rmcl/sailface/3dmodels/hull-experiments/hulltest7.FCStd

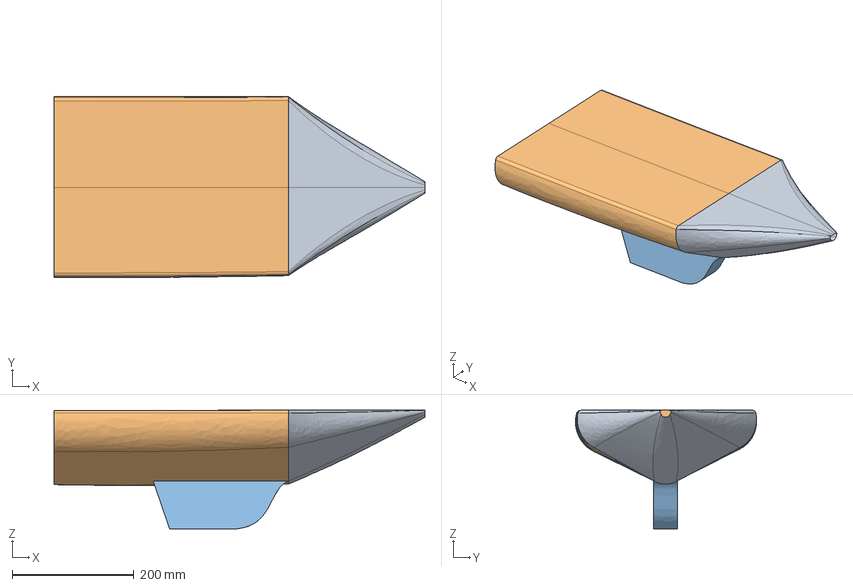
[picture p18: CAD file, 2022-07-22]
3dmodels/hull-experiments/hulltest7.FCStd
610.0 x 297.8 x 195.0 mm
KeelExtrude
