rmcl/sailface/3dmodels/hull-experiments/hulltest5.FCStd

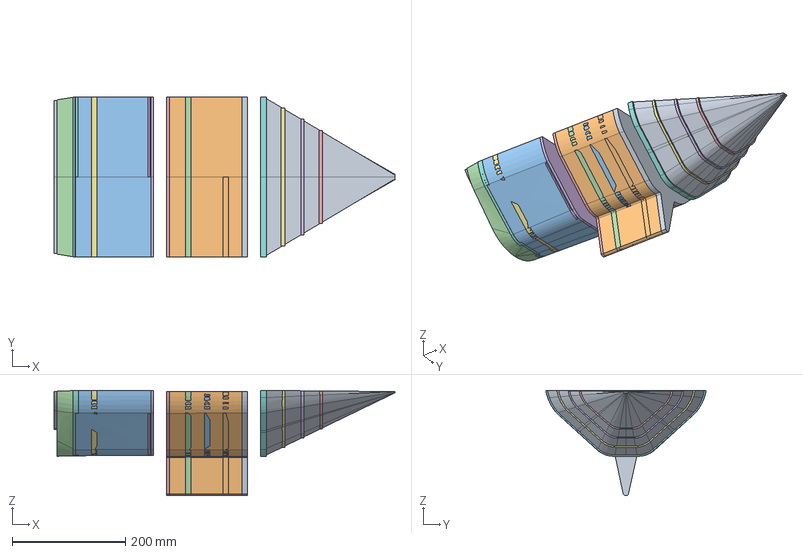
[picture p19: CAD file, 2022-07-22]
3dmodels/hull-experiments/hulltest5.FCStd
601.8 x 283.0 x 185.5 mm
