rmcl/sailface/3dmodels/Battery_VoltaicV70.FCStd

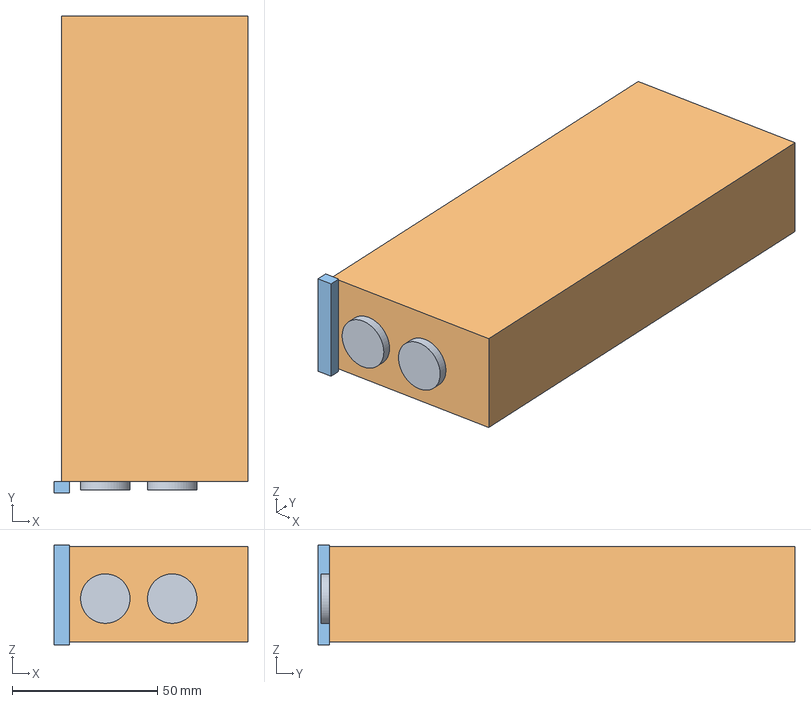
[picture p20: CAD file, 2022-07-22]
3dmodels/Battery_VoltaicV70.FCStd
66.6 x 164.0 x 34.3 mm
