rmcl/sailface/3dmodels/hull-experiments/hulltest8.FCStd

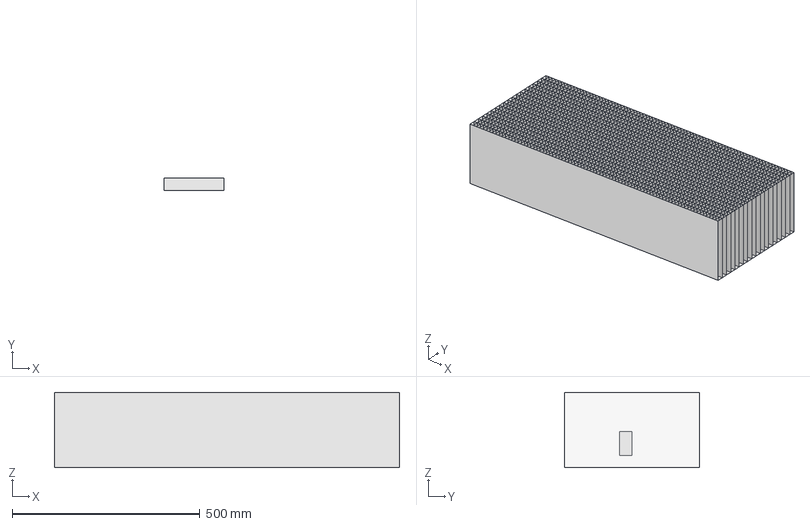
[picture p21: CAD file, 2022-07-22]
3dmodels/hull-experiments/hulltest8.FCStd
920.0 x 360.0 x 200.0 mm
battery
ExtrudeHullCrossectionSternBow
