rmcl/sailface/3dmodels/ServoSunFinderSF3218MG_v2.FCStd

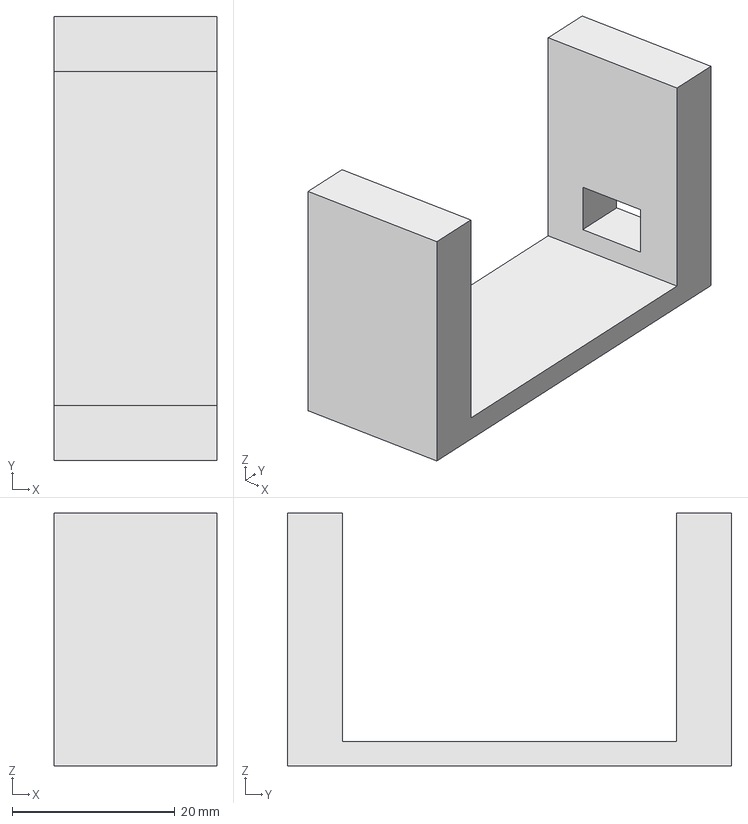
[picture p22: CAD file, 2022-07-22]
3dmodels/ServoSunFinderSF3218MG_v2.FCStd
20.0 x 54.5 x 31.0 mm
