rmcl/sailface/3dmodels/Prop_uxcell_prop_shaft.FCStd

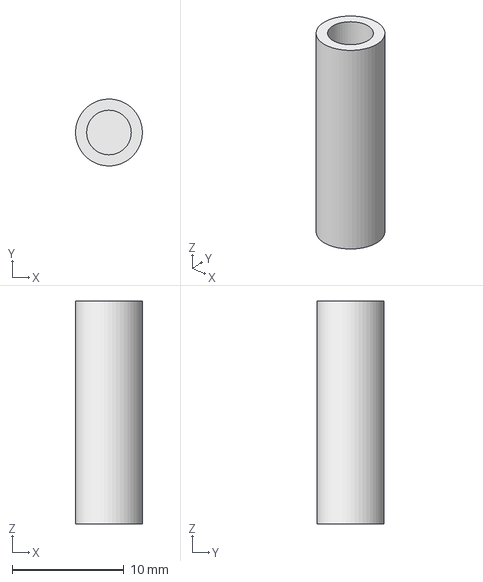
[picture p23: CAD file, 2022-07-22]
3dmodels/Prop_uxcell_prop_shaft.FCStd
5.99 x 6.00 x 20.0 mm
