rmcl/sailface/3dmodels/sunfounder_20kgSLDPRT.SLDPRT

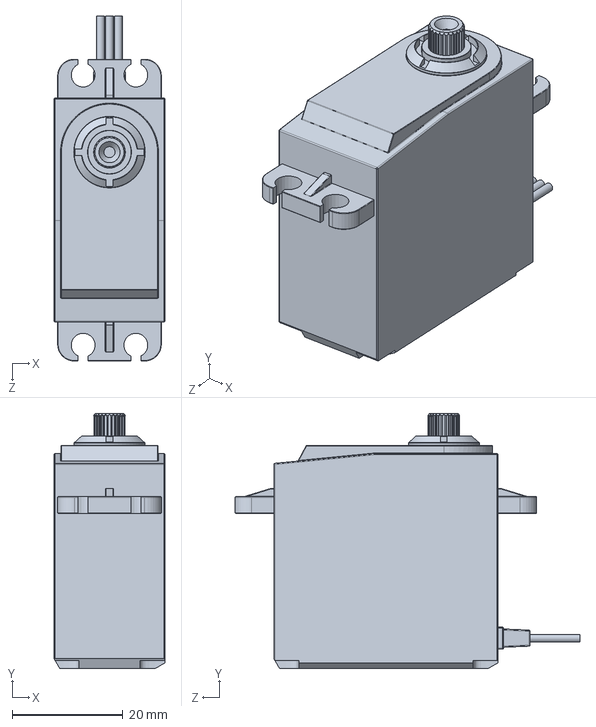
[picture p24: CAD file, 2022-07-22]
3dmodels/sunfounder_20kgSLDPRT.SLDPRT
20.0 x 46.0 x 62.2 mm
