rmcl/sailface/3dmodels/MotorHolderConnect_v1.FCStd

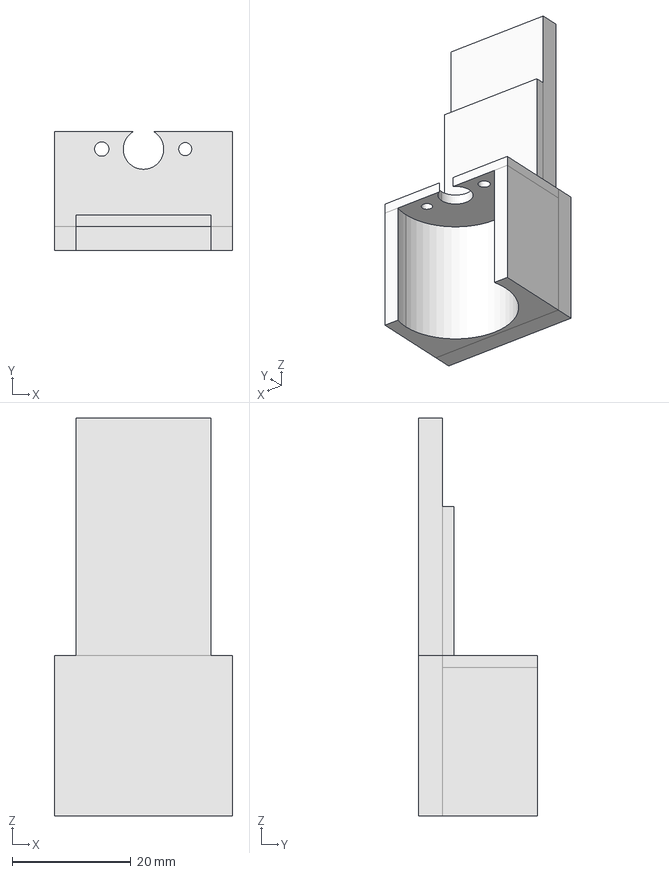
[picture p25: CAD file, 2022-07-22]
3dmodels/MotorHolderConnect_v1.FCStd
30.0 x 20.0 x 66.9 mm
