rmcl/sailface/3dmodels/internalstructure.FCStd

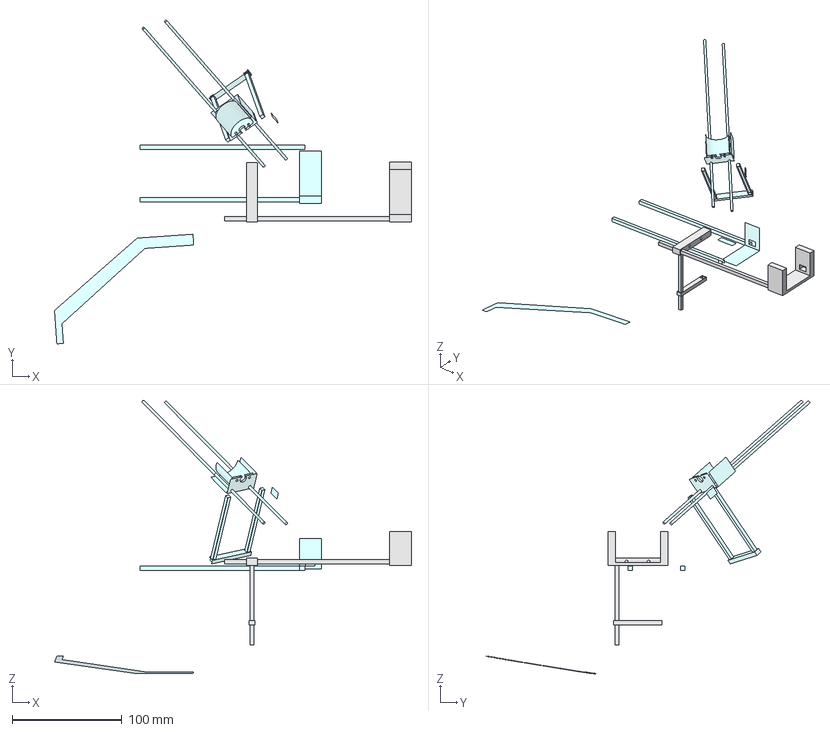
[picture p26: CAD file, 2022-07-22]
3dmodels/internalstructure.FCStd
324.8 x 294.6 x 248.7 mm
Element
Element001
Element002
Element003
Element004
Element005
Element006
Element007
Element008
Element009
Element011
Element014
Element015
Element018
_Element
_Element024
_Element026
_Element028
_Element030
_Element031
_Element032
_Element033
_Element034
_Element035
_Element037
_Element039
_Element041
_Element044
_Element046
_Element047
_Element050
_Element053
_Element054
_Element055
_Element056
_Element057
_Element061
_Element062
_Element064
_Element065
_Element066
_Element067
