rmcl/sailface/3dmodels/MotorAndHolder_v1.FCStd

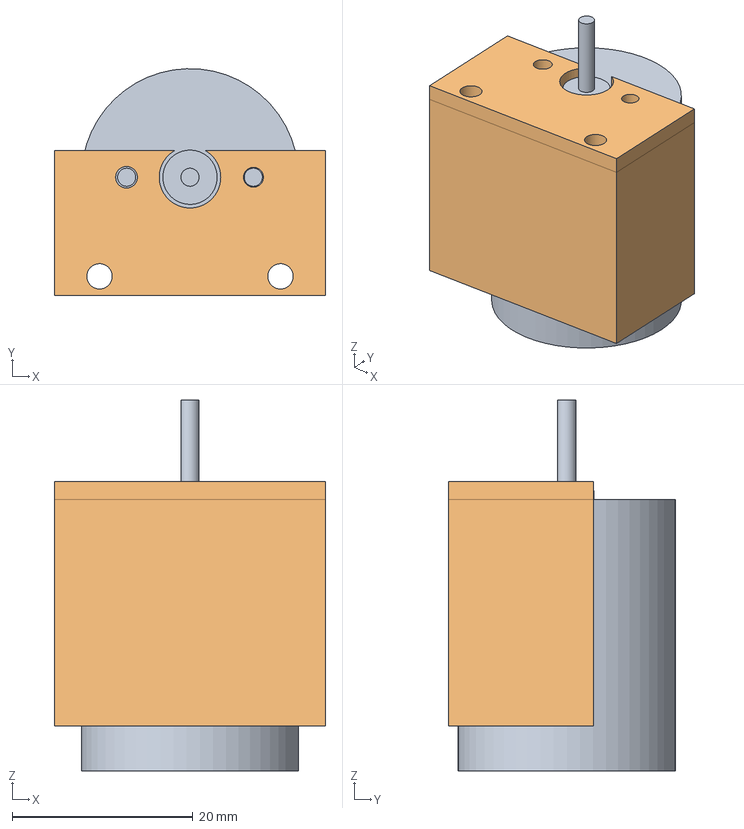
[picture p27: CAD file, 2022-07-22]
3dmodels/MotorAndHolder_v1.FCStd
30.0 x 25.0 x 41.0 mm
MotorBody
MotorHolderBody
MotorHolderBody001
