rmcl/sailface/3dmodels/rudder_coarse_1.FCStd

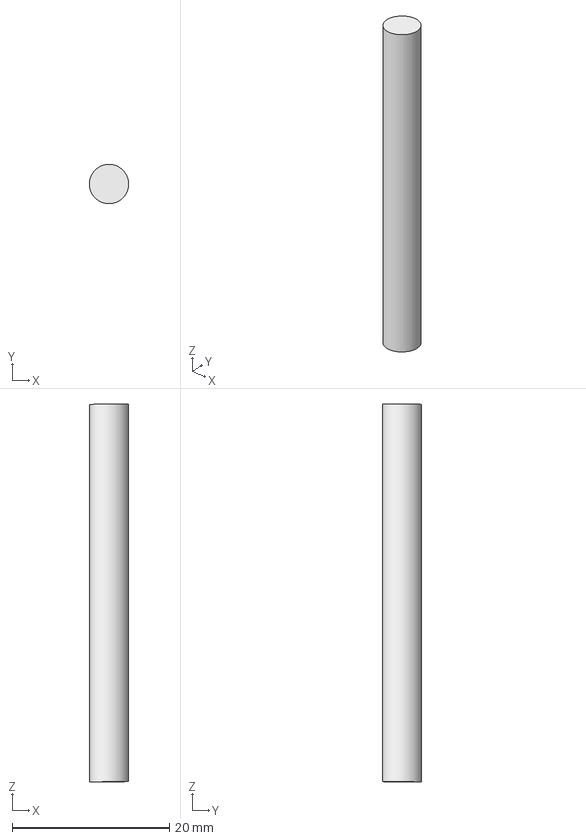
[picture p28: CAD file, 2022-07-22]
3dmodels/rudder_coarse_1.FCStd
5.00 x 5.00 x 48.1 mm
