rmcl/sailface/3dmodels/ServoHolder_v3.FCStd

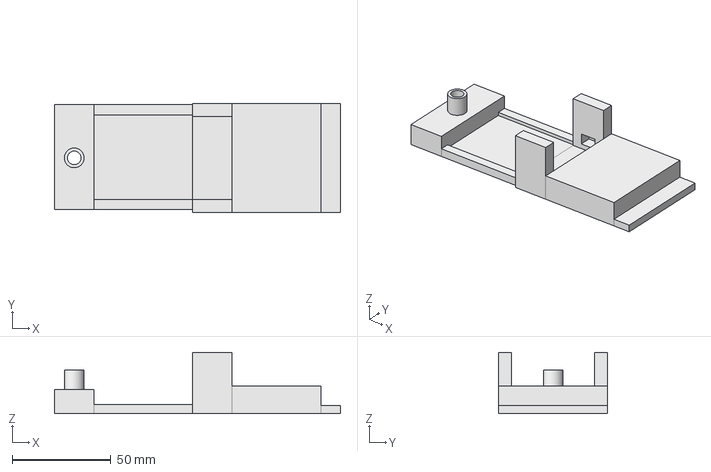
[picture p29: CAD file, 2022-07-22]
3dmodels/ServoHolder_v3.FCStd
145.0 x 55.5 x 31.0 mm
