rmcl/sailface/3dmodels/GPSAntennaHolder_v1.FCStd

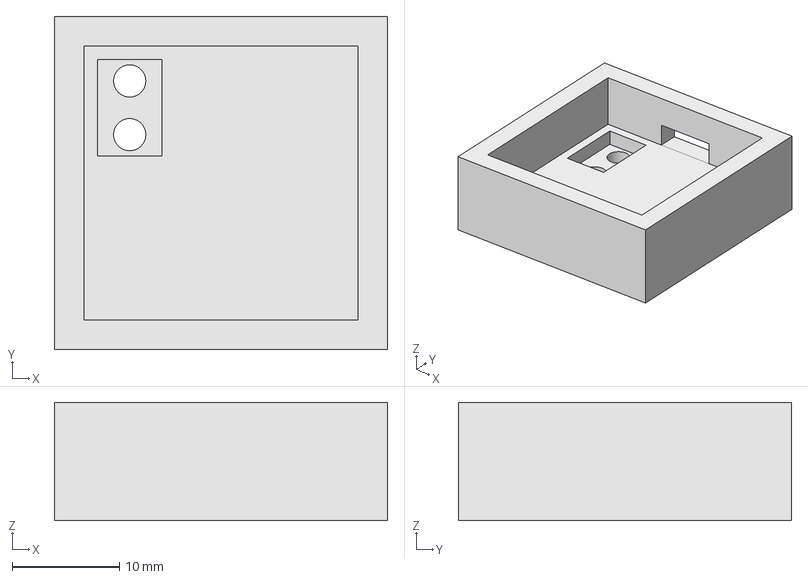
[picture p30: CAD file, 2022-07-22]
3dmodels/GPSAntennaHolder_v1.FCStd
31.0 x 31.0 x 11.0 mm
