rmcl/sailface/3dmodels/internalstructure_v2.FCStd

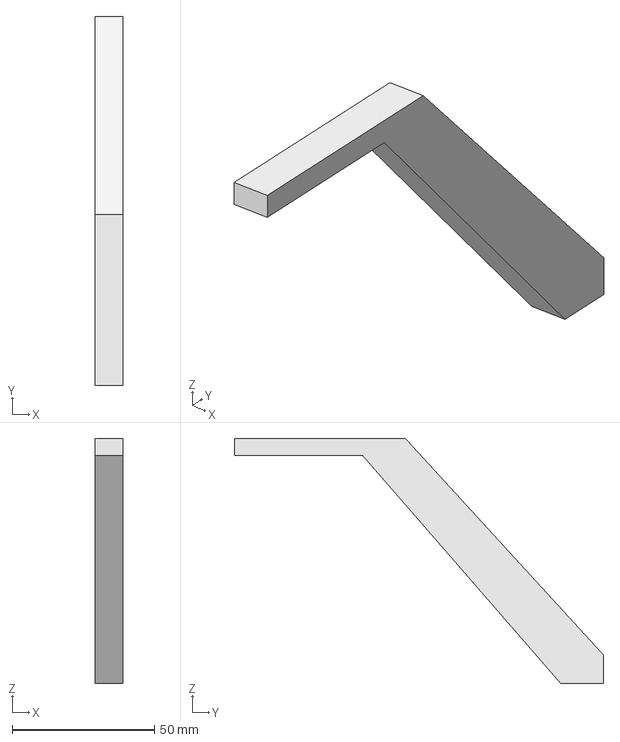
[picture p31: CAD file, 2022-07-22]
3dmodels/internalstructure_v2.FCStd
10.0 x 129.5 x 86.0 mm
