rmcl/sailface/sailface/iridium.cpp

/*

The goal of this module is to send and receive messages via the Iridium Short-Burst
Data services.

*/
#include "sailface.h"
#include "iridium.h"


void IridiumManager::initialize() {
    // SET THE SLEEP PIN TO OUTPUT
    pinMode(ROCKBLOCK_SLEEP_PIN, OUTPUT);
    digitalWrite(ROCKBLOCK_SLEEP_PIN, HIGH);

    pinMode(IRIDIUM_POWER_PIN, OUTPUT);
    digitalWrite(IRIDIUM_POWER_PIN, HIGH);

    // Setup the Ring Indicator Pin
    pinMode(ROCKBLOCK_RING_PIN, INPUT);

    IridiumSerial.begin(19200);
    modem.setPowerProfile(IridiumSBD::DEFAULT_POWER_PROFILE);
    modem.adjustATTimeout(45);

    // Retrieve values from persisted EEPROM data.
    lastTransmitTime = persistedData->getIridiumLastTransmitTime();
    updateFrequencyMinutes = persistedData->getIridiumTransmitFrequency();

    iridiumBusy = false;

    // If the Iridium was active before the power failure; start it up now.
    if (persistedData->getIridiumActive() == true) {
        wakeIridium();
    }
}

unsigned long IridiumManager::getLastTransmitTime() {
    return lastTransmitTime;
}
long IridiumManager::getUpdateFrequency() {
    return updateFrequencyMinutes;
}

bool IridiumManager::isIridiumActive() {
    return iridiumActive;
}

bool IridiumManager::isIridiumBusy() {
    return iridiumBusy;
}

void IridiumManager::wakeIridium() {
    digitalWrite(ROCKBLOCK_SLEEP_PIN, HIGH);

    if (bluetooth->isBluetoothActive()) {
        HardwareSerial *bluetoothDebug = bluetooth->getBluetoothSerial();
        bluetoothDebug->println("Attempting to begin Iridium modem");
    }

    // Begin satellite modem operation
    int errorCode = modem.begin();
    if (errorCode != ISBD_SUCCESS && errorCode != ISBD_ALREADY_AWAKE) {

        if (bluetooth->isBluetoothActive()) {
            HardwareSerial *bluetoothDebug = bluetooth->getBluetoothSerial();
            bluetoothDebug->println(
                String("ERR: Iridium begin failed CODE:") + \
                String(errorCode)
            );

            if (errorCode == ISBD_NO_MODEM_DETECTED) {
                bluetoothDebug->println("No modem detected: check wiring.");
            }
        }

        iridiumActive = false;
    } else {

        // TODO: DO WE WANT THIS!?
        // move this somewhere! SHOULD WE REALLY TURN THIS OFF? OR IS IT ALREADY OFF?
        modem.useMSSTMWorkaround(false);

        pollIridiumSignalQuality();
        iridiumActive = true;

        if (bluetooth->isBluetoothActive()) {
            HardwareSerial *bluetoothDebug = bluetooth->getBluetoothSerial();
            bluetoothDebug->println("INFO: Iridium successfully started.");
        }
    }

    // Persist if the Iridium is active into EEPROM memory.
    persistedData->storeIridiumActive(iridiumActive);

}

void IridiumManager::sleepIridium() {
    digitalWrite(ROCKBLOCK_SLEEP_PIN, LOW);
    iridiumActive = false;
}

void IridiumManager::pollIridiumSignalQuality() {
    int errorCode = modem.getSignalQuality(signalQuality);
    if (errorCode != ISBD_SUCCESS) {
        if (bluetooth->isBluetoothActive()) {
            HardwareSerial *bluetoothDebug = bluetooth->getBluetoothSerial();
            bluetoothDebug->println(
                String("ERR: Iridium Signal Quality Failure CODE:") + \
                String(errorCode)
            );
        }
        return;
    }

    if (bluetooth->isBluetoothActive()) {
        HardwareSerial *bluetoothDebug = bluetooth->getBluetoothSerial();
        bluetoothDebug->println(
            String("INFO: Iridium Signal Quality: ") + \
            String(signalQuality)
        );
    }
}

// The IridiumSBD will set the "Ring" pin to high if their are messages
// waiting for download. Return the number of messages waiting for
// download.
int IridiumManager::pollForIridiumRingAlerts() {
    bool ring = modem.hasRingAsserted();
    if (ring) {
        return modem.getWaitingMessageCount();
    }
    return 0;
}


IridiumStatusMessage IridiumManager::buildStatusMessage() {
    IridiumStatusMessage message;

    PositionInfo curPosition = position->getCurPosition();
    Waypoint activeWaypoint = navigation->getActiveWaypoint();

    PowerInfo powerInfo;
    power->getPowerInfo(&powerInfo);

    message.batteryVoltage = powerInfo.batteryVoltage * 10; // multiple by ten to convert to short int
    message.latitude = curPosition.latitude;
    message.longitude = curPosition.longitude;
    message.waypointLatitude = activeWaypoint.latitude;
    message.waypointLongitude = activeWaypoint.longitude;
    message.propSpeed = prop->getPropellerSpeed();
    return message;
}

/*
unsigned long IridiumManager::getIridiumTime() {
    //time_t curTime;
    //modem.getSystemTime(curTime);
    return -1;
}
*/

bool IridiumManager::shouldTransmitStatus() {

    // Todo: Maybe replace this with getIridiumTime();
    unsigned long curTime = millis(); 
    if ((curTime - lastTransmitTime) < (updateFrequencyMinutes * 60000)) {
        return false;
    }
    return true;
}

//
// Send and Receive messages from Iridium.
int IridiumManager::sendStatusReceiveCommandMessage(
    IridiumStatusMessage *txMessage,
    IridiumCommandMessage *rxCommandMessage
) {
    size_t txMessageSize = 0;
    if (txMessage != NULL) {
        txMessageSize = sizeof(*txMessage);
    }

    iridiumBusy = true;

    size_t rxBufferSize = sizeof(*rxCommandMessage);
    int errorCode = modem.sendReceiveSBDBinary(
        (uint8_t*)txMessage,
        txMessageSize,
        (uint8_t*)rxCommandMessage,
        rxBufferSize);

    iridiumBusy = false;

    if (errorCode != ISBD_SUCCESS) {
        if (bluetooth->isBluetoothActive()) {
            HardwareSerial *bluetoothDebug = bluetooth->getBluetoothSerial();
            bluetoothDebug->println(
                String("ERROR: sendReceiveSBDBinary error ") + \
                String(errorCode)
            );
        }

        if (errorCode == ISBD_SENDRECEIVE_TIMEOUT) {
            //sendDebugMessage("Try again with a better view of the sky.");
            //TODO: Maybe we put a retry in place?
        }

        return 0;

    } else {
        if (bluetooth->isBluetoothActive()) {
            HardwareSerial *bluetoothDebug = bluetooth->getBluetoothSerial();
            bluetoothDebug->println(
                String("INFO: sendReceiveSBDBinary success ERROR CODE: ") + \
                String(errorCode) + \
                String("\n RX BUF SIZE: " + rxBufferSize)
            );
        }

        // Update the last transmit time to be when the Iridium Send/Receive command
        // completes.
        lastTransmitTime = millis();
        persistedData->storeIridiumLastTransmitTime(lastTransmitTime);

        int messageCount = modem.getWaitingMessageCount();
        if (rxBufferSize > 0) {
            // If we received a message add it to number of messages waiting.
            messageCount += 1;
        }

        return messageCount;
    }
}

// Poll for messages via the RockBlock Ring Alert Pin
int IridiumManager::pollForCommandMessages(bool forceTransmitStatus) {
    if (!iridiumActive) {
        return 0;
    }

    bool shouldTransmit = shouldTransmitStatus();

    int messageCount = pollForIridiumRingAlerts();
    if (messageCount == 0 && !shouldTransmit && !forceTransmitStatus && !iridiumBusy) {
        return 0;
    }

    if (bluetooth->isBluetoothActive()) {
        HardwareSerial *bluetoothDebug = bluetooth->getBluetoothSerial();
        bluetoothDebug->println("Iridium attempting to RX/TX");
    }

    IridiumStatusMessage statusMessage = buildStatusMessage();

    // Is this required? Can i just do &statusMessage later?
    IridiumStatusMessage *txStatusMessagePtr = &statusMessage;

    IridiumCommandMessage firstReceivedCommand;

    while (true) {
        messageCount = sendStatusReceiveCommandMessage(
            txStatusMessagePtr,
            &firstReceivedCommand);

        if (messageCount > 0) {
            processCommandMessage(&firstReceivedCommand);
        }

        if (messageCount > 1) {
            // there are more messages to retrieve
            // dont send status again
            txStatusMessagePtr = NULL;
        } else {
            // otherwise we have sent and retrieved all messages so we are done
            return 1;
        }
    }


    // Current message + some number of outstanding messages.
    return 1 + messageCount;
}


void IridiumManager::processCommandMessage(IridiumCommandMessage *commandMessage) {

    if (bluetooth->isBluetoothActive()) {
        HardwareSerial *bluetoothDebug = bluetooth->getBluetoothSerial();
        bluetoothDebug->println(
            String("Received Iridium Command Message\n") + \
            String("PROP SPEED: ") + \
            String(commandMessage->propSpeed) + \
            String(" SAT TX FREQ: ") + \
            String(commandMessage->updateFrequencyMinutes) + \
            String("\nNAV TO WAYPOINT ENABLED: ") + \
            String(commandMessage->navigateToWaypoint)  +\
            String("WAYPOINT ACTION: ") + \
            String(commandMessage->waypointAction) + \
            String("NUM PTS: ") + \
            String(commandMessage->numWaypoints)
        );

        for (int index = 0; index < commandMessage->numWaypoints; index++) {
            bluetoothDebug->println(
                String("  LAT:") + \
                String(commandMessage->waypoints[index].latitude) + \
                String(",") + \
                String(commandMessage->waypoints[index].longitude) + \
                String("  RADIUS:") + \
                String(commandMessage->waypoints[index].allowedRadiusMeters)
            );
        }
    }

    prop->setPropellerSpeed(commandMessage->propSpeed);

    updateFrequencyMinutes = commandMessage->updateFrequencyMinutes;
    persistedData->storeIridiumTransmitFrequency(updateFrequencyMinutes);

    switch(commandMessage->waypointAction) {
        case WAYPOINT_APPEND:
            // Append new waypoint to existing.
            navigation->updateWaypoints(
                commandMessage->waypoints,
                commandMessage->numWaypoints,
                true);

            break;
        case WAYPOINT_OVERWRITE:
            // Clear existing waypoints and append
            navigation->updateWaypoints(
                commandMessage->waypoints,
                commandMessage->numWaypoints,
                false);
            break;

        case WAYPOINT_NO_CHANGE:
        default:
            break;
    }

    if (commandMessage->navigateToWaypoint == true) {
        navigation->startNavigatingToWaypoint();
    } else {
        navigation->stopNavigatingToWaypoint();
    }
}

/* Iridium Debug Routines

void ISBDConsoleCallback(IridiumSBD *device, char c) {
    Serial.write(c);
}

void ISBDDiagsCallback(IridiumSBD *device, char c) {
    Serial.write(c);
}

*/
