rmcl/sailface/sailface/bluetooth_command.h

#ifndef _BLUETOOTH_COMMAND
#define _BLUETOOTH_COMMAND

#include <Arduino.h>
#include "SerialCommands.h"

#define BLUETOOTH_ENABLE_PIN 9

//#define COMM_MAX_COMMAND_LEN 500

#define SERIAL_COMMANDS_DEBUG false


/* Commands */
void cmdUnrecognized(SerialCommands* sender, const char* cmd);
void cmdHelp(SerialCommands* sender);
void cmdStatus(SerialCommands* sender);
void cmdSetRudder(SerialCommands* sender);
void cmdStartProp(SerialCommands* sender);
void cmdStopProp(SerialCommands* sender);
void cmdStartIridium(SerialCommands* sender);
void cmdSleepIridium(SerialCommands* sender);
void cmdPollIridium(SerialCommands* sender);
void cmdCalibrationMPU(SerialCommands* sender);
void cmdStartNavWaypoint(SerialCommands* sender);
void cmdStopNavWaypoint(SerialCommands* sender);
void cmdWaypointAppend(SerialCommands* sender);
void cmdSetPIDParams(SerialCommands* sender);

class BluetoothCommand {

    private:
        bool bluetoothActive;

        // Serial2 on the Mega is pins TX2 pin 16 and RX2 pin 17
        // Bluetooth RXD -> TX2 pin 16
        // Bluetooth TXD -> RX2 pin 17
        HardwareSerial &bluetoothSerial = Serial2;

        char serialCommandBuffer[32];

        SerialCommands bluetoothSerialCommands{
            &bluetoothSerial,
            serialCommandBuffer,
            sizeof(serialCommandBuffer),
            "\n",
            " "
        };

        /* Command Calls */
        SerialCommand blueCmdHelp{"HELP", cmdHelp};
        SerialCommand blueCmdStatus{"STATUS", cmdStatus};
        SerialCommand blueCmdSetRudder{"RUDDER", cmdSetRudder};
        SerialCommand blueCmdStartProp{"ENGAGE", cmdStartProp};
        SerialCommand blueCmdStopProp{"STOP", cmdStopProp};
        SerialCommand blueCmdStartIridium{"SATSTART", cmdStartIridium};
        SerialCommand blueCmdSleepIridium{"SATSLEEP", cmdSleepIridium};
        SerialCommand blueCmdPollIridium{"SATPOLL", cmdPollIridium};
        SerialCommand blueCmdCalibrateMPU{"MPUCAL", cmdCalibrationMPU};
        SerialCommand blueCmdStartNavWaypoint{"NAVSTART", cmdStartNavWaypoint};
        SerialCommand blueCmdStopNavWaypoint{"NAVSTOP", cmdStopNavWaypoint};
        SerialCommand blueCmdSetPIDParams{"NAVPID",cmdSetPIDParams};
        SerialCommand blueCmdWaypointAppend{"WPA", cmdWaypointAppend};


    public:
        void initialize();

        void pollForBluetoothCommandMessages();
        bool isBluetoothActive();
        HardwareSerial *getBluetoothSerial();
};
#endif
