rmcl/sailface/arduino_examples/motorcontrol1/motorcontrol1.ino

//This example drives a robot in left and right arcs, driving in an overall wiggly course.
//  It demonstrates the variable control abilities. When used with a RedBot chassis,
//  each turn is about 90 degrees per drive.
//
//  Pin 8 can be grounded to disable motor movement, for debugging.

#include <Arduino.h>
#include <stdint.h>
#include "SCMD.h"
#include "SCMD_config.h" //Contains #defines for common SCMD register names and values
#include "Wire.h"

SCMD myMotorDriver; //This creates the main object of one motor driver and connected slaves.

void setup()
{
  pinMode(8, INPUT_PULLUP); //Use to halt motor movement (ground)

  Serial.begin(9600);
  Serial.println("Starting sketch.");

  //***** Configure the Motor Driver's Settings *****//
  //  .commInter face can be I2C_MODE or SPI_MODE
  myMotorDriver.settings.commInterface = I2C_MODE;
  //myMotorDriver.settings.commInterface = SPI_MODE;

  //  set address if I2C configuration selected with the config jumpers
  myMotorDriver.settings.I2CAddress = 0x5A; //config pattern "0101" on board for address 0x5A

  //  set chip select if SPI selected with the config jumpers
  myMotorDriver.settings.chipSelectPin = 10;

  //*****initialize the driver get wait for idle*****//
  while ( myMotorDriver.begin() != 0xA9 ) //Wait until a valid ID word is returned
  {
    Serial.println( "ID mismatch, trying again" );
    delay(500);
  }
  Serial.println( "ID matches 0xA9" );

  //  Check to make sure the driver is done looking for slaves before beginning
  Serial.print("Waiting for enumeration...");
  while ( myMotorDriver.ready() == false );
  Serial.println("Done.");
  Serial.println();

  //*****Set application settings and enable driver*****//

  //Uncomment code for motor 0 inversion
  //while( myMotorDriver.busy() );
  //myMotorDriver.inversionMode(0, 1); //invert motor 0

  //Uncomment code for motor 1 inversion
  while ( myMotorDriver.busy() ); //Waits until the SCMD is available.
  myMotorDriver.inversionMode(1, 1); //invert motor 1

  while ( myMotorDriver.busy() );
  myMotorDriver.enable(); //Enables the output driver hardware

}

#define LEFT_MOTOR 0
#define RIGHT_MOTOR 1
void loop()
{

    //***** Operate the Motor Driver *****//
    //  This walks through all 34 motor positions driving them forward and back.
    //  It uses .setDrive( motorNum, direction, level ) to drive the motors.

    myMotorDriver.setDrive( LEFT_MOTOR, 0, 80);

    //delay(10000);

    //myMotorDriver.setDrive( LEFT_MOTOR, 0, 200);

    //pass setDrive() a motor number, direction as 0(call 0 forward) or 1, and level from 0 to 255
    //myMotorDriver.setDrive( LEFT_MOTOR, 0, 0); //Stop motor
    //myMotorDriver.setDrive( RIGHT_MOTOR, 0, 0); //Stop motor
    ///while (digitalRead(8) == 0); //Hold if jumper is placed between pin 8 and ground

}
